Gramatiik/AppelClient/Sources/Palet/VW_test1/Config.h

#ifndef _CONFIG
#define _CONFIG

String NUMPALET = "01";
int DELAY = 5; // temps de desactivation apres reception de trame
int PINLED = 12; // numero pin LED
int PINVIBRO = 10; // numero pin moteur vibration

#endif
